ammonshepherd/led-watch/first-blog-post/assets/post-media/led-watch/watch_battery.jpg

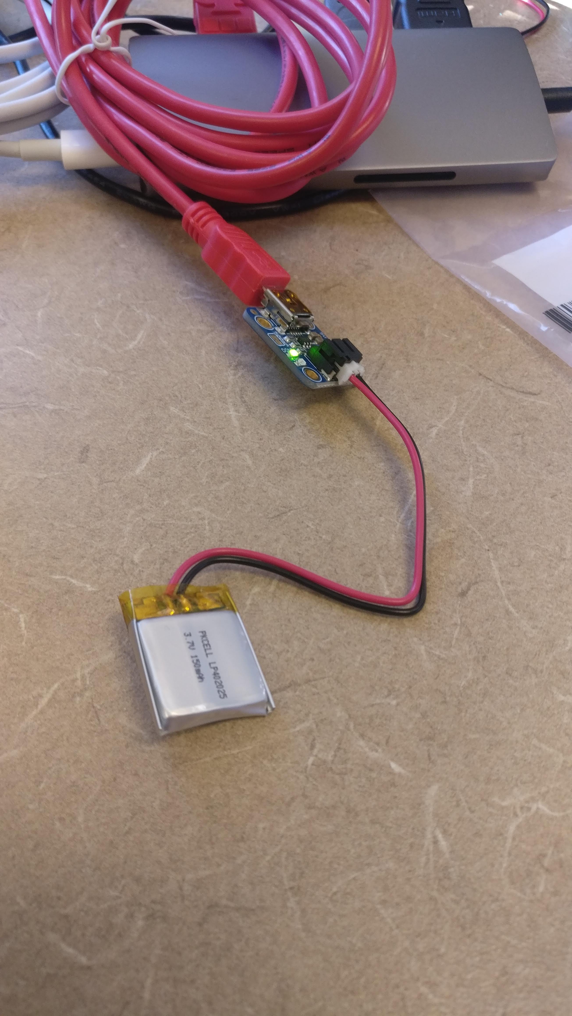
first-blog-post/assets/post-media/led-watch/watch_battery.jpg
