ammonshepherd/led-watch/first-blog-post/assets/post-media/led-watch/watch_cases.jpg

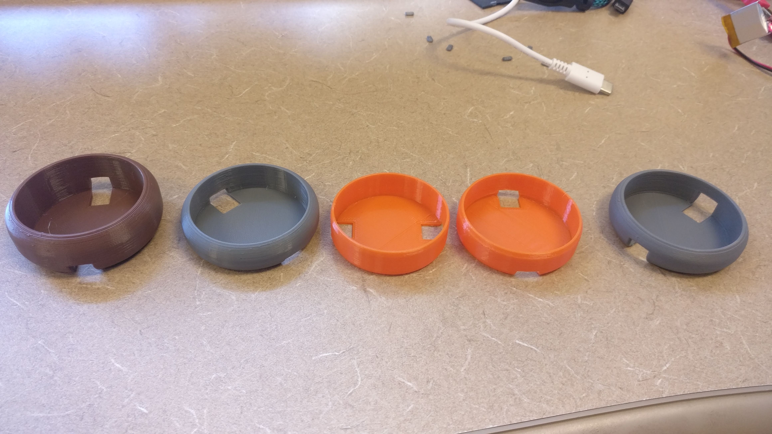
first-blog-post/assets/post-media/led-watch/watch_cases.jpg
