ammonshepherd/led-watch/second-blog-post/assets/post-media/led-watch-complete/blue-red.jpg

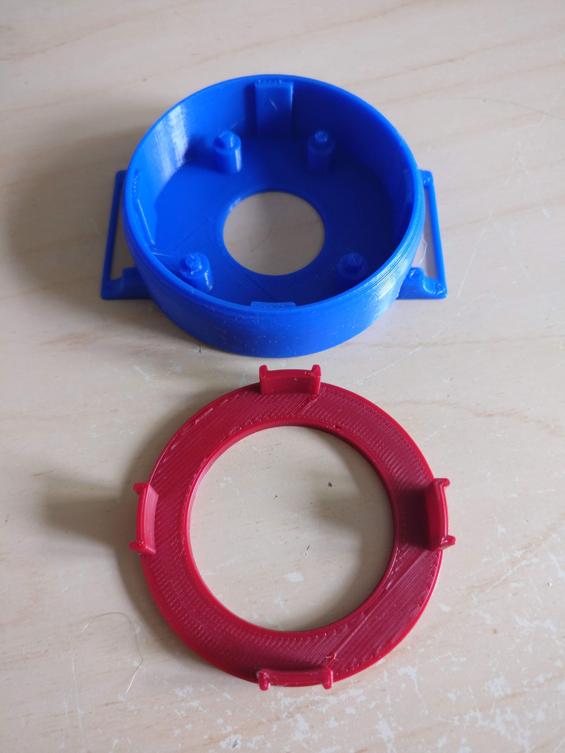
second-blog-post/assets/post-media/led-watch-complete/blue-red.jpg
