ammonshepherd/led-watch/second-blog-post/assets/post-media/led-watch-complete/blue.jpg

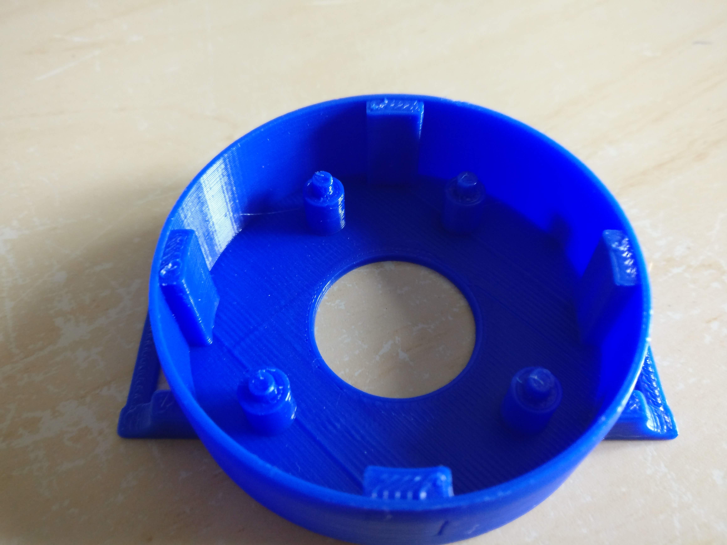
second-blog-post/assets/post-media/led-watch-complete/blue.jpg
