ammonshepherd/led-watch/second-blog-post/assets/post-media/led-watch-complete/completed.jpg

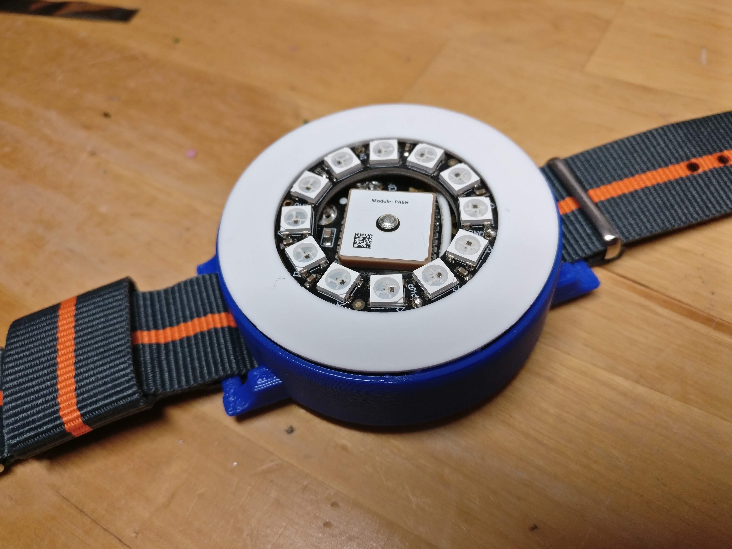
second-blog-post/assets/post-media/led-watch-complete/completed.jpg
