ammonshepherd/led-watch/second-blog-post/assets/post-media/led-watch-complete/exploded-view.jpg

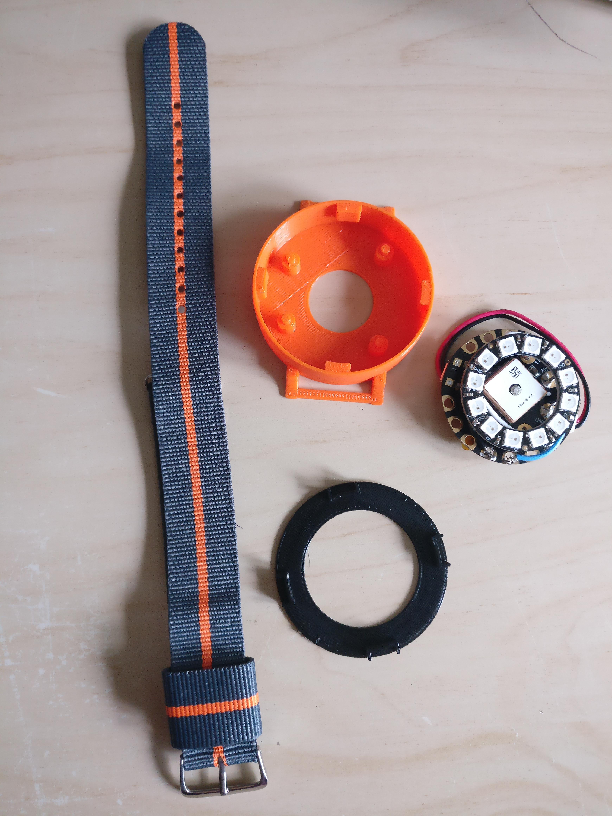
second-blog-post/assets/post-media/led-watch-complete/exploded-view.jpg
