ammonshepherd/led-watch/second-blog-post/assets/post-media/led-watch-complete/good-watch.jpg

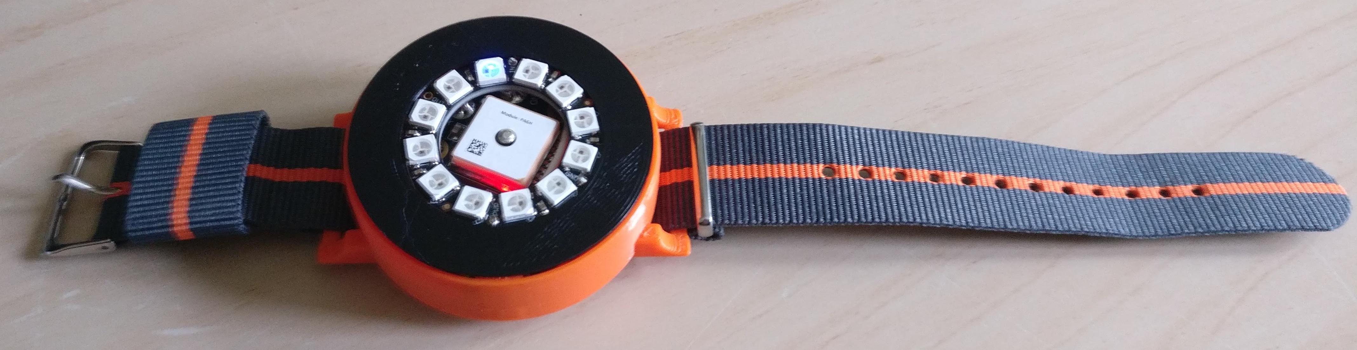
second-blog-post/assets/post-media/led-watch-complete/good-watch.jpg
