ammonshepherd/led-watch/second-blog-post/assets/post-media/led-watch-complete/guts-out.jpg

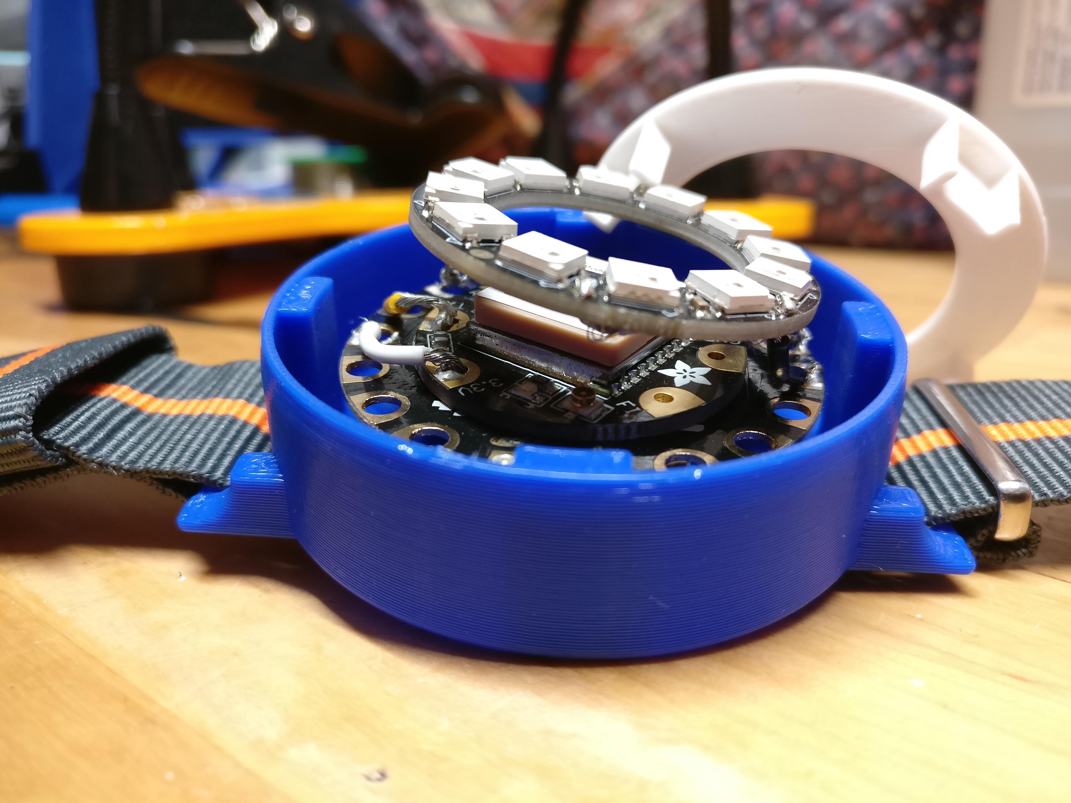
second-blog-post/assets/post-media/led-watch-complete/guts-out.jpg
