ammonshepherd/led-watch/second-blog-post/assets/post-media/led-watch-complete/lid-on.jpg

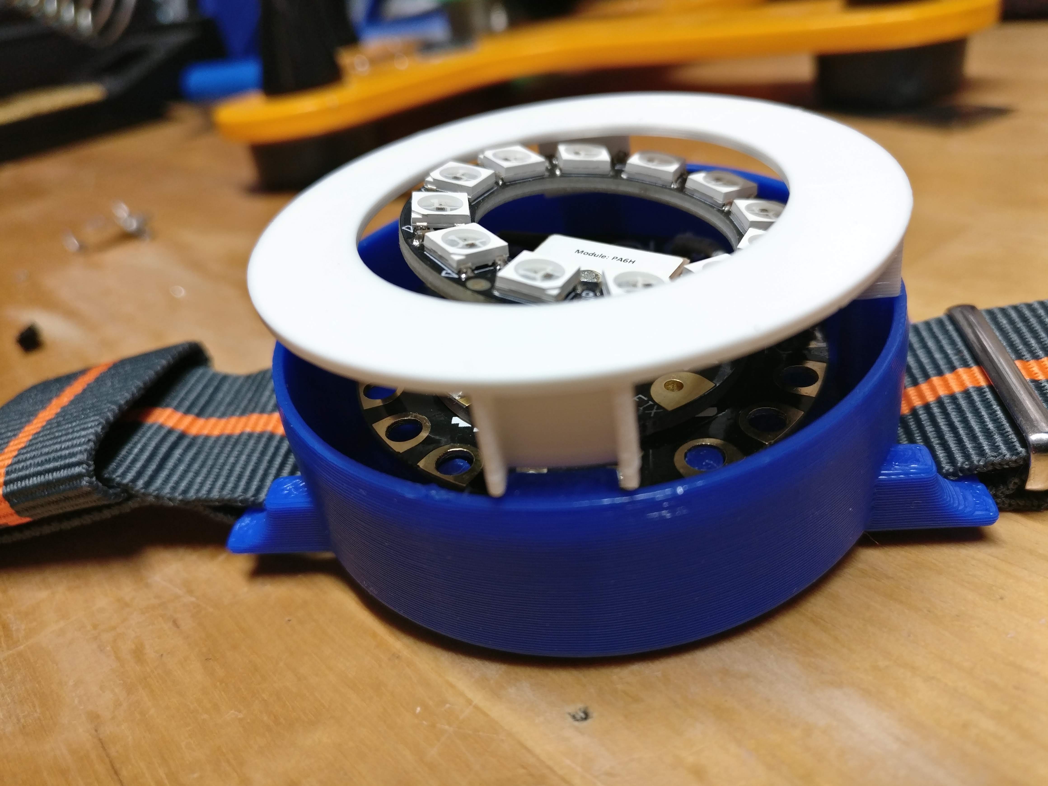
second-blog-post/assets/post-media/led-watch-complete/lid-on.jpg
