ammonshepherd/led-watch/second-blog-post/assets/post-media/led-watch-complete/orange-lid-off.jpg

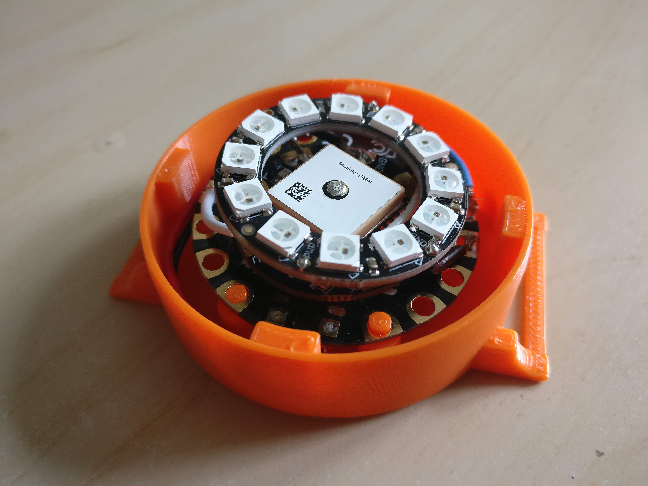
second-blog-post/assets/post-media/led-watch-complete/orange-lid-off.jpg
