ammonshepherd/led-watch/second-blog-post/assets/post-media/led-watch-complete/orange-watch.jpg

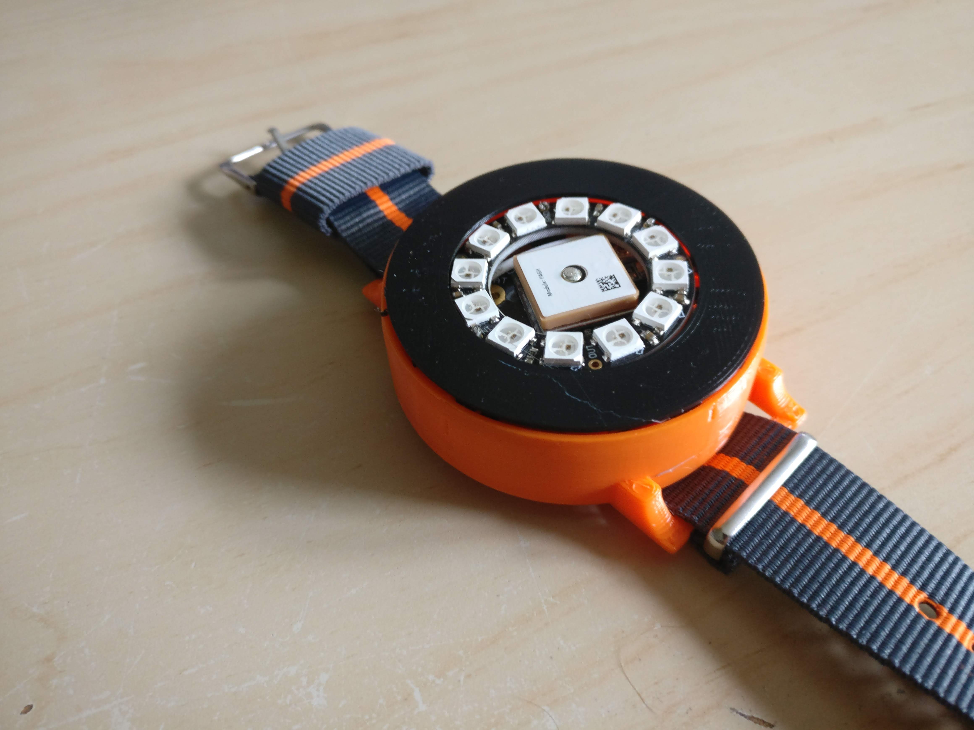
second-blog-post/assets/post-media/led-watch-complete/orange-watch.jpg
