ammonshepherd/led-watch/second-blog-post/assets/post-media/led-watch-complete/orange.jpg

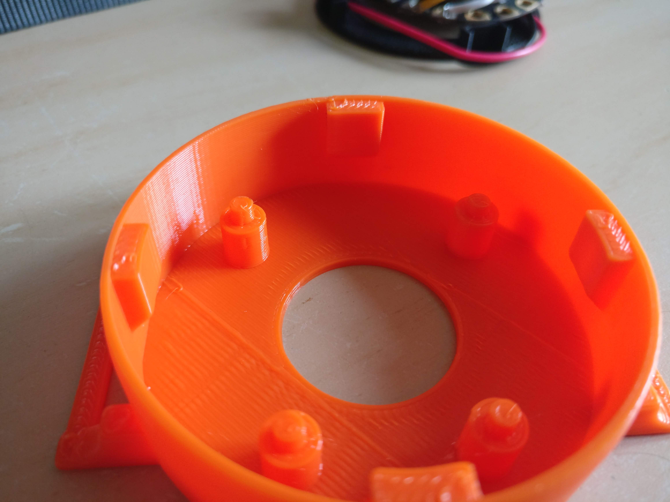
second-blog-post/assets/post-media/led-watch-complete/orange.jpg
