ammonshepherd/led-watch/second-blog-post/assets/post-media/led-watch-complete/pink.jpg

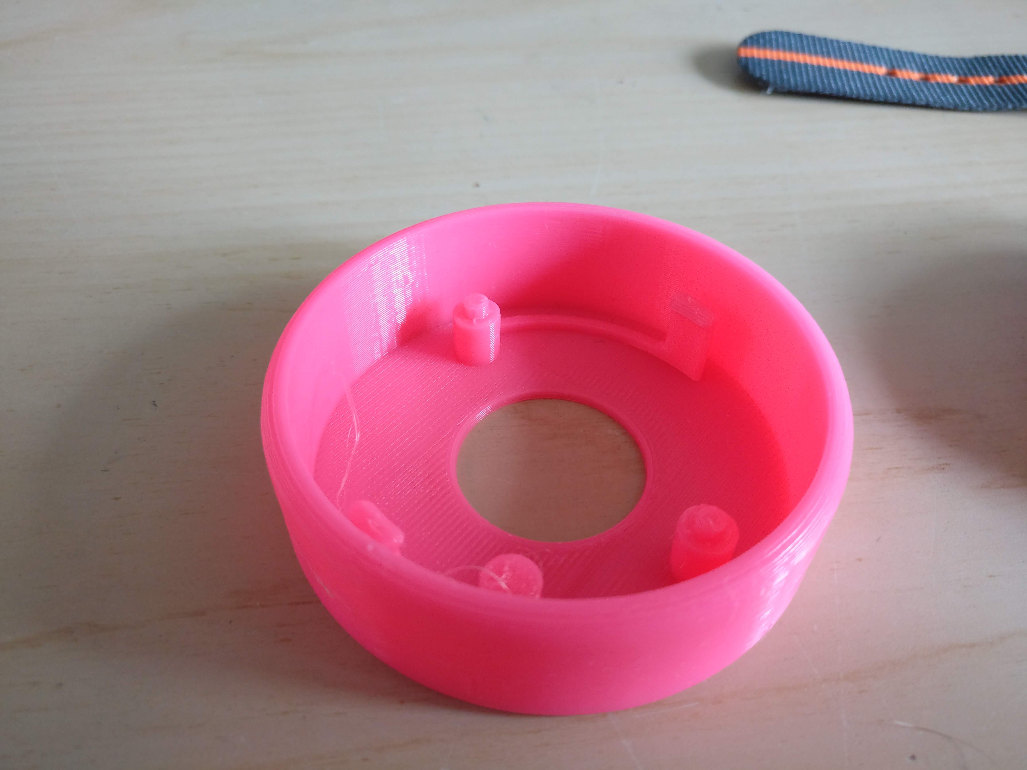
second-blog-post/assets/post-media/led-watch-complete/pink.jpg
