ammonshepherd/led-watch/second-blog-post/assets/post-media/led-watch-complete/prusa-slicer.png

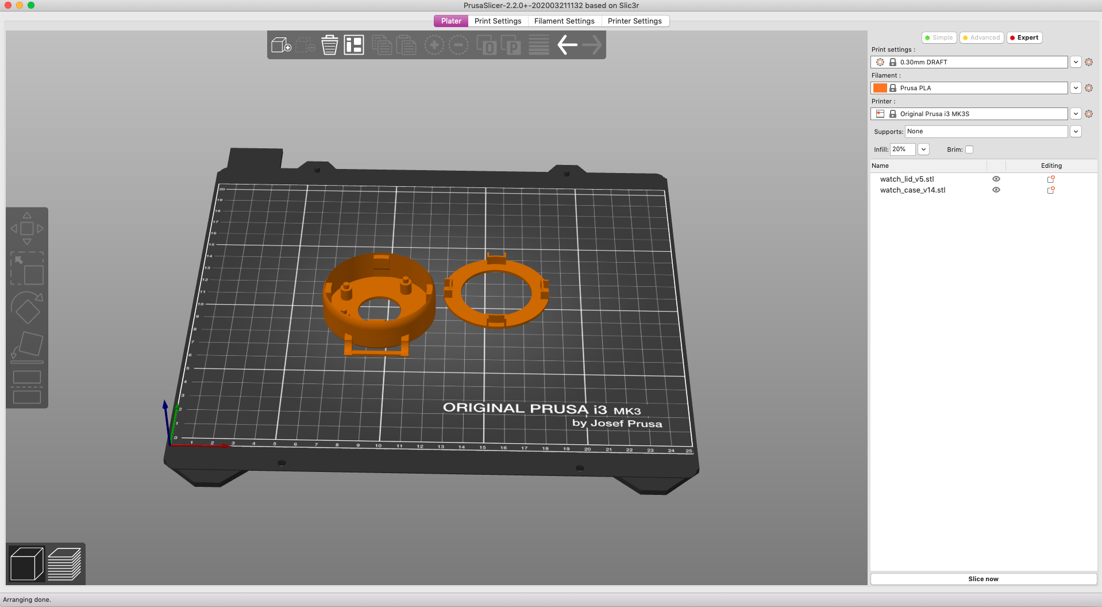
second-blog-post/assets/post-media/led-watch-complete/prusa-slicer.png
