ammonshepherd/led-watch/second-blog-post/assets/post-media/led-watch-complete/red-red-2.jpg

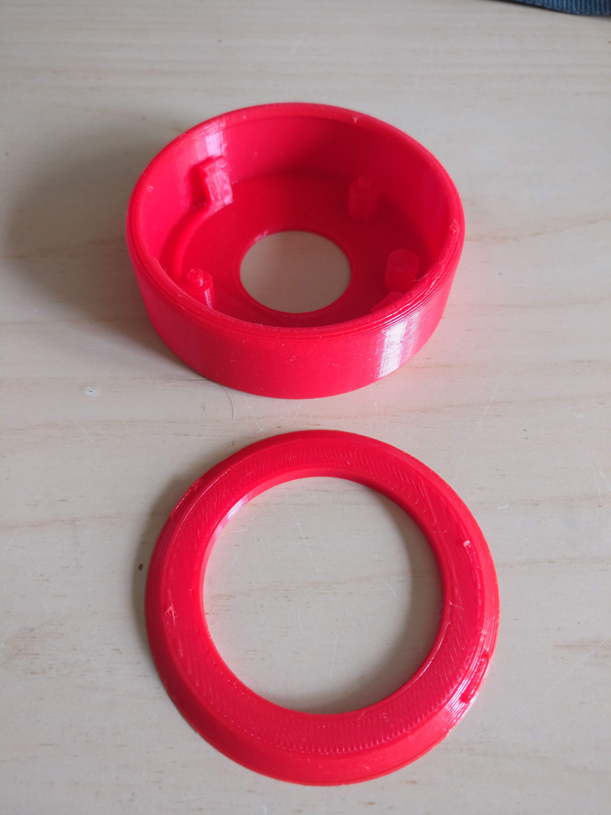
second-blog-post/assets/post-media/led-watch-complete/red-red-2.jpg
