ammonshepherd/led-watch/second-blog-post/assets/post-media/led-watch-complete/through-the-looking-glass.jpg

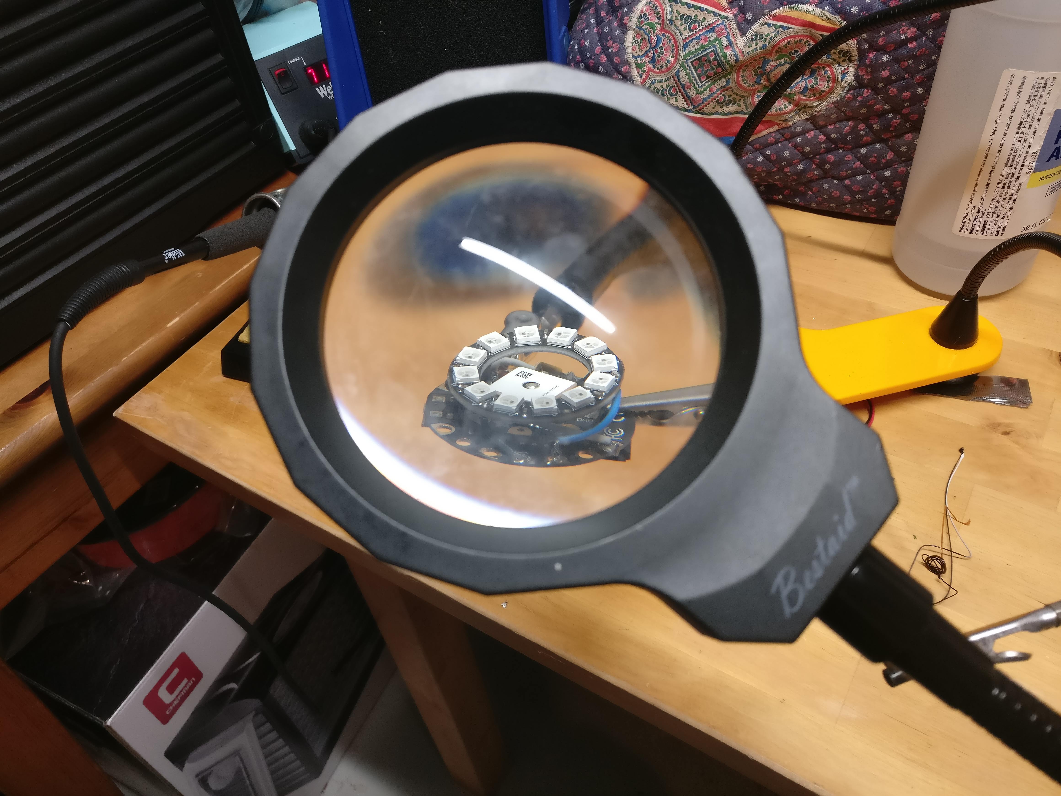
second-blog-post/assets/post-media/led-watch-complete/through-the-looking-glass.jpg
