ammonshepherd/led-watch/second-blog-post/assets/post-media/led-watch-complete/two-lights.jpg

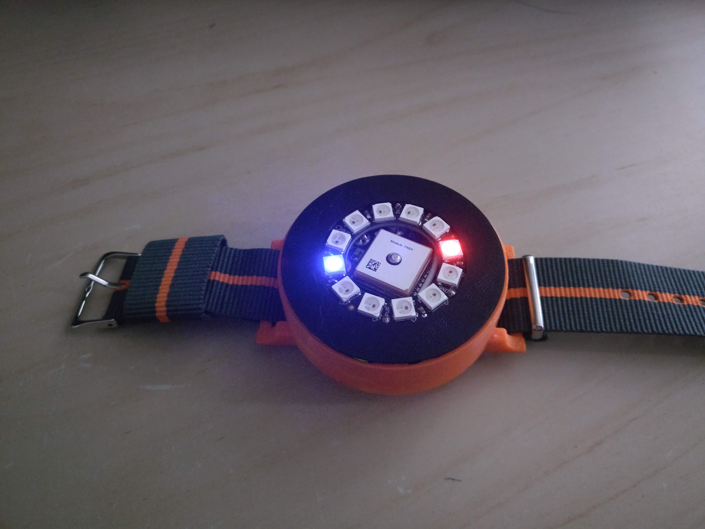
second-blog-post/assets/post-media/led-watch-complete/two-lights.jpg
