ammonshepherd/led-watch/second-blog-post/assets/post-media/led-watch-complete/vid.gif

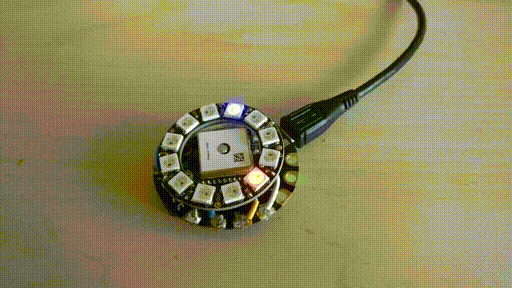
second-blog-post/assets/post-media/led-watch-complete/vid.gif
