ammonshepherd/led-watch/second-blog-post/assets/post-media/led-watch-complete/work-bench.jpg

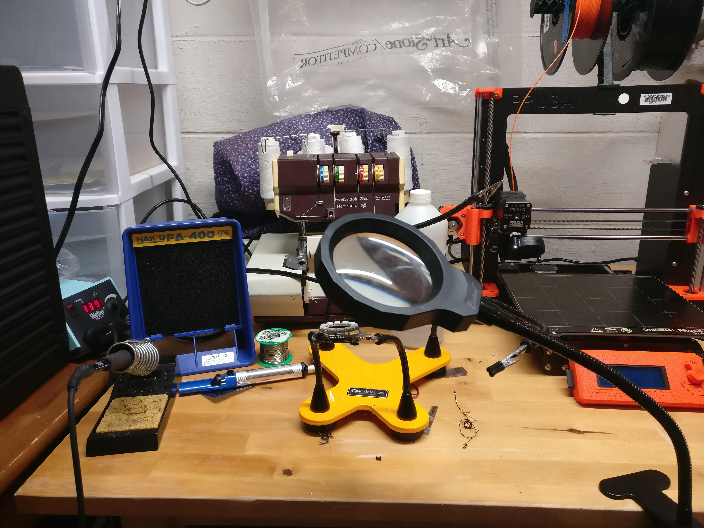
second-blog-post/assets/post-media/led-watch-complete/work-bench.jpg
