ammonshepherd/led-watch/second-blog-post/assets/post-media/led-watch-complete/parts-1.jpg

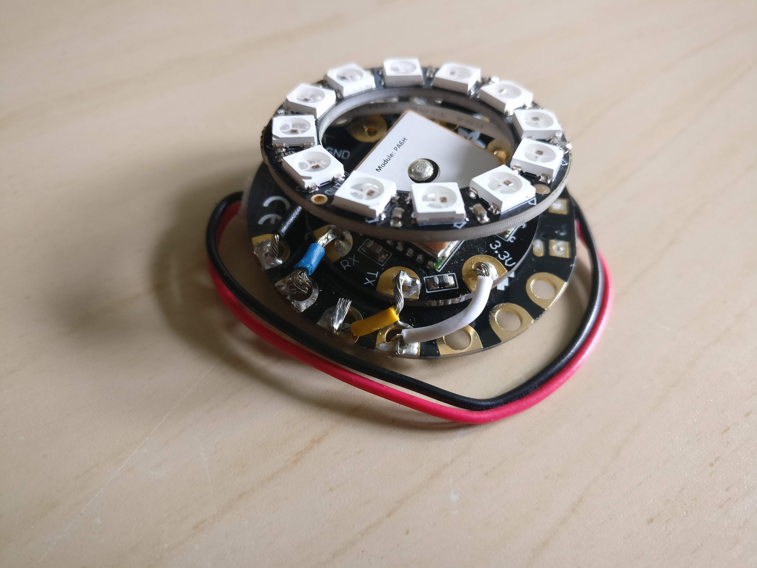
second-blog-post/assets/post-media/led-watch-complete/parts-1.jpg
