ammonshepherd/led-watch/second-blog-post/assets/post-media/led-watch-complete/parts-3.jpg

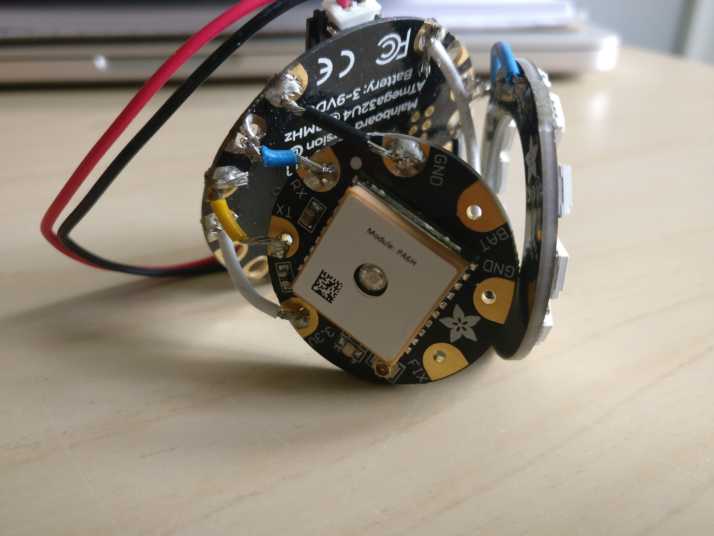
second-blog-post/assets/post-media/led-watch-complete/parts-3.jpg
